polykit/kosmo-spring-reverb-driver/kosmo-spring-reverb-driver-pcb-large.jpg

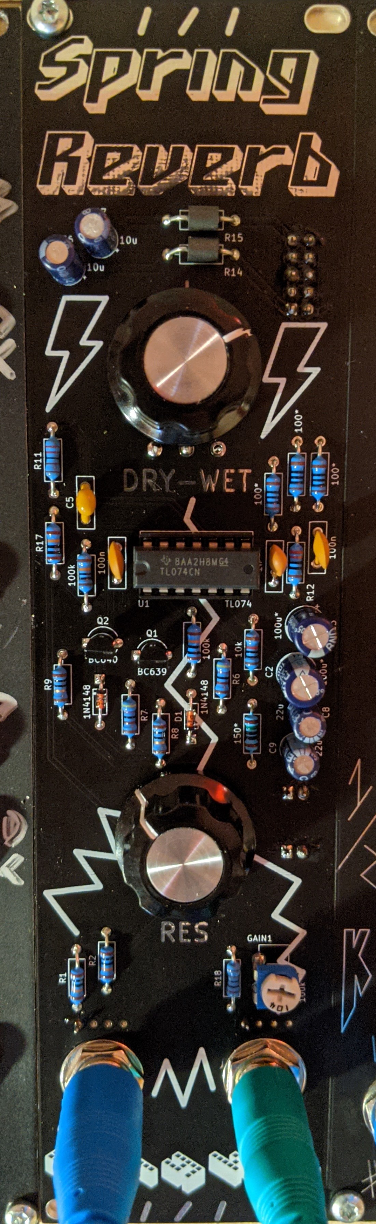
kosmo-spring-reverb-driver-pcb-large.jpg
